ruofeidu/VRSurus/images/bark-diffuse.jpg

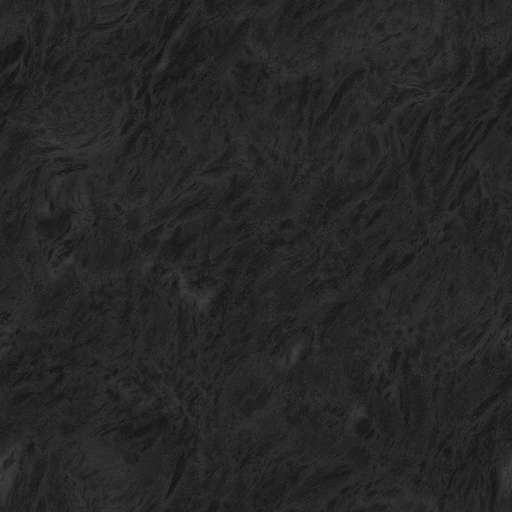
images/bark-diffuse.jpg
