ruofeidu/VRSurus/images/cloudsphere.jpg

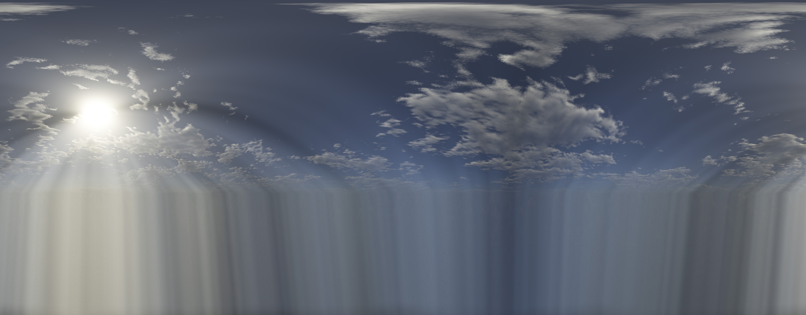
images/cloudsphere.jpg
