ruofeidu/VRSurus/images/fire.png

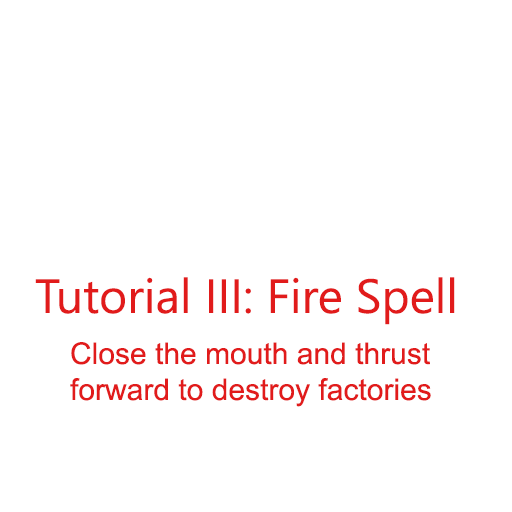
images/fire.png
