ruofeidu/VRSurus/images/leaves-shadow.jpg

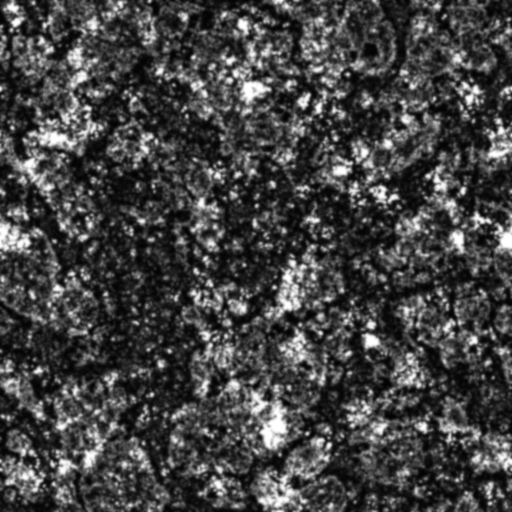
images/leaves-shadow.jpg
