ruofeidu/VRSurus/images/trunk.jpg

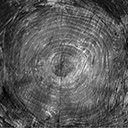
images/trunk.jpg
