ruofeidu/VRSurus/images/water.png

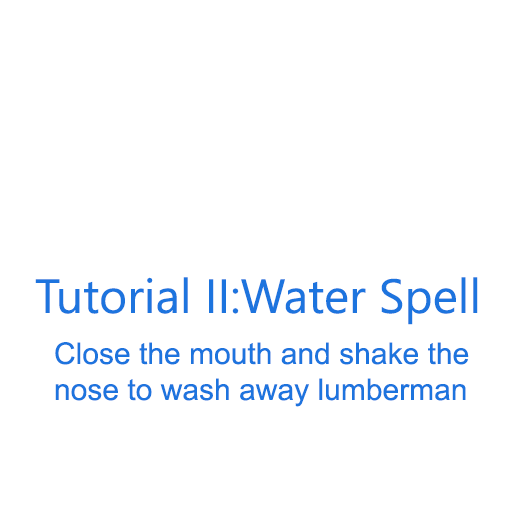
images/water.png
