ruofeidu/VRSurus/images/instruction.png

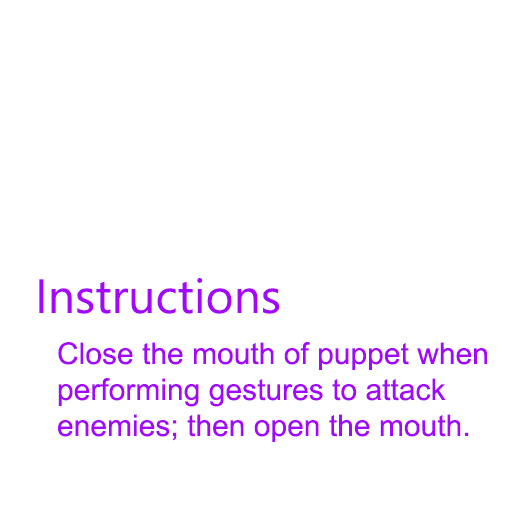
images/instruction.png
